Kazxu/Single-Pair-Ethernet-For-Industrial-Use/EVAL_ADIN1110/Core/Src/tcpecho_raw.c

/*
 * Copyright (c) 2001-2004 Swedish Institute of Computer Science.
 * All rights reserved. 
 * 
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
 * This file is part of and a contribution to the lwIP TCP/IP stack.
 *
 * Credits go to Adam Dunkels (and the current maintainers) of this software.
 *
 * Christiaan Simons rewrote this file to get a more stable echo example.
 */

/**
 * @file
 * TCP echo server example using raw API.
 *
 * Echos all bytes sent by connecting client,
 * and passively closes when client is done.
 *
 *
 *
 * EDITED FOR OUR BACHELOR USAGE, mixed code and etc - DAVY POON
 */

#include "lwip/opt.h"
#include "lwip/debug.h"
#include "lwip/stats.h"
#include "tcpecho_raw.h"
#include "lwip/opt.h"
#include "lwip/sys.h"
#include "main.h"

static u32_t last_send_time = 0;  // Timestamp of the last sent message

static char *EVAL_STRING_MSG = " \n YOUR MSG: TILKOBLET YAHOO \n" ;

struct tcp_pcb *global_tpcb = NULL;  // Definition of the global TCP control block
static char *shared_buffer = NULL; // Shared buffer between TCP Echo server and Main
#if LWIP_TCP && LWIP_CALLBACK_API




enum tcpecho_raw_states
{
  ES_NONE = 0,
  ES_ACCEPTED,
  ES_RECEIVED,
  ES_CLOSING
};

struct tcpecho_raw_state
{
  u8_t state;
  u8_t retries;
  struct tcp_pcb *pcb;
  /* pbuf (chain) to recycle */
  struct pbuf *p;
};

static void
tcpecho_raw_free(struct tcpecho_raw_state *es)
{
  if (es != NULL) {
    if (es->p) {
      /* free the buffer chain if present */
      pbuf_free(es->p);
    }

    mem_free(es);
  }  
}

static void
tcpecho_raw_close(struct tcp_pcb *tpcb, struct tcpecho_raw_state *es)
{
  tcp_arg(tpcb, NULL);
  tcp_sent(tpcb, NULL);
  tcp_recv(tpcb, NULL);
  tcp_err(tpcb, NULL);
  tcp_poll(tpcb, NULL, 0);

  tcpecho_raw_free(es);

  tcp_close(tpcb);
}

static void
tcpecho_raw_send(struct tcp_pcb *tpcb, struct tcpecho_raw_state *es)
{
  struct pbuf *ptr;
  err_t wr_err = ERR_OK;
 
  while ((wr_err == ERR_OK) &&
         (es->p != NULL) && 
         (es->p->len <= tcp_sndbuf(tpcb))) {
    ptr = es->p;

    /* enqueue data for transmission */
    wr_err = tcp_write(tpcb, ptr->payload, ptr->len, 1);
    if (wr_err == ERR_OK) {
      u16_t plen;

      plen = ptr->len;
      /* continue with next pbuf in chain (if any) */
      es->p = ptr->next;
      if(es->p != NULL) {
        /* new reference! */
        pbuf_ref(es->p);
      }
      /* chop first pbuf from chain */
      pbuf_free(ptr);
      /* we can read more data now */
      tcp_recved(tpcb, plen);
    } else if(wr_err == ERR_MEM) {
      /* we are low on memory, try later / harder, defer to poll */
      es->p = ptr;
    } else {
      /* other problem ?? */
    }
  }
}

static void
tcpecho_raw_error(void *arg, err_t err)
{
  struct tcpecho_raw_state *es;

  LWIP_UNUSED_ARG(err);

  es = (struct tcpecho_raw_state *)arg;

  tcpecho_raw_free(es);
}
// Define 'last_send_time'
// Function poll callback for the TCP echo server. Timer baserer seg til polling interval set i initialization.
static err_t tcpecho_raw_poll(void *arg, struct tcp_pcb *tpcb) {

	// Retrieve the state structure til current TCP connection, passed as 'arg' basert på default LWIP -raw API.
	struct tcpecho_raw_state *es = (struct tcpecho_raw_state *)arg;

	// Get the current system time in milliseconds from the lwIP system clock.
	u32_t current_time = sys_now();

    // Check if 500ms
    if (current_time - last_send_time >= 500) {


       // const char *msg = "Hello, this is a timed message! \n";
    	const char *msg = buffer;

        // Check if there is enough space in the TCP send buffer to send the message.
        if (tcp_sndbuf(tpcb) > strlen(msg)) {

        	 // Write the message to the TCP send buffer.
        	/* pcb: The TCP control block (PCB) -> Den init
			   data: Pointer to the data to be sent.
               len: Length of the data in bytes.
               flags: Control flag -> operation av tcp_write.*/
            tcp_write(tpcb, msg, strlen(msg), TCP_WRITE_FLAG_COPY);// Ensure that the message is actually sent out over the network.
            /*
             Efficient buffer management, including appropriate use of flags like TCP_WRITE_FLAG_COPY,
             is essential to ensure that your TCP/IP stack remains responsive and efficient,
             avoiding potential pitfalls like buffer overruns or unnecessary delays in data transmission.
             - https://lwip.fandom.com/wiki/Tuning_TCP
             */

            // Calls the internal lwIP function to process and send TCP packets.
            tcp_output(tpcb); //OUTPUT fra LWIP


            last_send_time = current_time;  // Update the last send time -> current time
        }
    }

    // Check if -> echo server state == not null, som betyr connection is still active
    if (es != NULL) {
    	 // Check if hvis pending data har ikke blitt sent.
        if (es->p != NULL) {
            // send remaining data
        	// Logic to send remaining data ikke blitt implementert enda
        	// "Typically, this would involve checking the TCP send buffer space and calling tcp_write as needed." - LWIP
        }
        // any additional handling --> HER KAN VI ADDE MER FUNKSJON
        // inkludert  connection maintenance, error checks, etc.

    } else { // If the state == null, problem med connection (e.g., it was unexpectedly closed).

    	// Abort the TCP connection to clean up the PCB and release resources.
        tcp_abort(tpcb);
        return ERR_ABRT;
    }
    // If everything processed correctly and the connection is still active, return ERR_OK.
    return ERR_OK;
}


static err_t
tcpecho_raw_sent(void *arg, struct tcp_pcb *tpcb, u16_t len)
{
  struct tcpecho_raw_state *es;

  LWIP_UNUSED_ARG(len);

  es = (struct tcpecho_raw_state *)arg;
  es->retries = 0;

  if(es->p != NULL) {
    /* still got pbufs to send */
    tcp_sent(tpcb, tcpecho_raw_sent);
    tcpecho_raw_send(tpcb, es);
  } else {
    /* no more pbufs to send */
    if(es->state == ES_CLOSING) {
      tcpecho_raw_close(tpcb, es);
    }
  }
  return ERR_OK;
}
static err_t
tcpecho_raw_recv(void *arg, struct tcp_pcb *tpcb, struct pbuf *p, err_t err) {
    struct tcpecho_raw_state *es;
    err_t ret_err;

    LWIP_ASSERT("arg != NULL", arg != NULL);
    es = (struct tcpecho_raw_state *)arg;

    if (p == NULL) {
        // Connection closed
        es->state = ES_CLOSING;
        if (es->p == NULL) {
            tcpecho_raw_close(tpcb, es);
        } else {
            tcpecho_raw_send(tpcb, es);
        }
        ret_err = ERR_OK;
    } else if (err != ERR_OK) {
        // Handle receive error
        if (p != NULL) {
            pbuf_free(p);
        }
        ret_err = err;
    } else {
        // Process received data
        if (es->state == ES_ACCEPTED) {
            es->state = ES_RECEIVED;
        }
        send_eval_string_msg(tpcb); // Send the EVAL_STRING_MSG

        // Echo logic as before
        if (es->p != NULL) {
            pbuf_cat(es->p, p);
        } else {
            es->p = p;
            pbuf_ref(p);
        }
        tcpecho_raw_send(tpcb, es);
        ret_err = ERR_OK;
    }
    return ret_err;
}


static err_t
tcpecho_raw_accept(void *arg, struct tcp_pcb *newpcb, err_t err)
{
  err_t ret_err;
  struct tcpecho_raw_state *es;

  LWIP_UNUSED_ARG(arg);
  if ((err != ERR_OK) || (newpcb == NULL)) {
    return ERR_VAL;
  }

  /* Unless this pcb should have NORMAL priority, set its priority now.
     When running out of pcbs, low priority pcbs can be aborted to create
     new pcbs of higher priority. */
  tcp_setprio(newpcb, TCP_PRIO_MIN);

  es = (struct tcpecho_raw_state *)mem_malloc(sizeof(struct tcpecho_raw_state));
  if (es != NULL) {
    es->state = ES_ACCEPTED;
    es->pcb = newpcb;
    es->retries = 0;
    es->p = NULL;
    /* pass newly allocated es to our callbacks */
    tcp_arg(newpcb, es);
    tcp_recv(newpcb, tcpecho_raw_recv);
    tcp_err(newpcb, tcpecho_raw_error);
    tcp_poll(newpcb, tcpecho_raw_poll, 0);
    tcp_sent(newpcb, tcpecho_raw_sent);
    ret_err = ERR_OK;
  } else {
    ret_err = ERR_MEM;
  }
  return ret_err;
}

// Initialization function to set up the PCB and polling
void tcpecho_raw_init(char *buffer) {
	//LAGER TCP  PCB -> TCP SOCKET
	shared_buffer = buffer;
    global_tpcb = tcp_new();
    if (global_tpcb != NULL) {  // Check if the PCB was successfully created.
        err_t err = tcp_bind(global_tpcb, IP_ADDR_ANY, 66);
        // Bind the newly created PCB object to any IP address on port 66.

        if (err == ERR_OK) {// Check if the binding was successful.

        	// Putter PCB == LISTEN state, convert til listen PCB -> accept incoming connections.
        	global_tpcb = tcp_listen(global_tpcb);

        	 // Set up a callback function som event handler -> incoming connections.
        	 // `tcp_accept` assigns a function to be called when a new connection is established.
            tcp_accept(global_tpcb, tcpecho_raw_accept);

            // Set up a callback function to be called periodically
            // polling callback brukt som regularly check/event handle tasks som å  sende periodic/timed messages
            // The `1` = polling frequency; in the lwIP stack ->> multiplied av TCP timer interval
            // (typically 500 ms), so a value of `1`  = 500 ms.
            tcp_poll(global_tpcb, tcpecho_raw_poll, 1);  // Set the poll interval
        }
    }
}



void send_eval_string_msg(struct tcp_pcb *tpcb) {
    if (tpcb != NULL && tcp_sndbuf(tpcb) > strlen(EVAL_STRING_MSG)) {
        tcp_write(tpcb, EVAL_STRING_MSG, strlen(EVAL_STRING_MSG), TCP_WRITE_FLAG_COPY);
        tcp_output(tpcb);  // Data sendt Instant, brukes kanskje senere, vet ikke, har bare med tilfelle
    }
}



#endif /* LWIP_TCP && LWIP_CALLBACK_API */
