Kazxu/Single-Pair-Ethernet-For-Industrial-Use/EVAL_ADIN1110/Core/Src/usart.c

/**
  ******************************************************************************
  * File Name          : USART.c
  * Description        : This file provides code for the configuration
  *                      of the USART instances.
  ******************************************************************************
  * @attention
  *
  * <h2><center>&copy; Copyright (c) 2020 STMicroelectronics.
  * All rights reserved.</center></h2>
  *
  * This software component is licensed by ST under BSD 3-Clause license,
  * the "License"; You may not use this file except in compliance with the
  * License. You may obtain a copy of the License at:
  *                        opensource.org/licenses/BSD-3-Clause
  *
  ******************************************************************************
  */

/**
  *  Portions Copyright (c) 2020, 2021 Analog Devices, Inc.
  */

/* Includes ------------------------------------------------------------------*/
#include "usart.h"

UART_HandleTypeDef huart1;
DMA_HandleTypeDef hdma_usart1_tx;
DMA_HandleTypeDef hdma_usart1_rx;
/* USART1 init function */

HAL_StatusTypeDef MX_USART1_UART_Init(void)
{

  huart1.Instance = USART1;
  huart1.Init.BaudRate = 115200;
  huart1.Init.WordLength = UART_WORDLENGTH_8B;
  huart1.Init.StopBits = UART_STOPBITS_1;
  huart1.Init.Parity = UART_PARITY_NONE;
  huart1.Init.Mode = UART_MODE_TX_RX;
  huart1.Init.HwFlowCtl = UART_HWCONTROL_NONE;
  huart1.Init.OverSampling = UART_OVERSAMPLING_16;
  huart1.Init.OneBitSampling = UART_ONE_BIT_SAMPLE_DISABLE;
  huart1.Init.ClockPrescaler = UART_PRESCALER_DIV1;
  huart1.AdvancedInit.AdvFeatureInit = UART_ADVFEATURE_NO_INIT;

  return HAL_UART_Init(&huart1);
}

void HAL_UART_MspInit(UART_HandleTypeDef* uartHandle)
{

  GPIO_InitTypeDef GPIO_InitStruct = {0};
  if(uartHandle->Instance==USART1)
  {
    /* USART1 clock enable */
    __HAL_RCC_USART1_CLK_ENABLE();

    /**USART1 GPIO Configuration
    PA10     ------> USART1_RX
    PA9     ------> USART1_TX
    */
    GPIO_InitStruct.Pin = GPIO_PIN_10|GPIO_PIN_9;
    GPIO_InitStruct.Mode = GPIO_MODE_AF_PP;
    GPIO_InitStruct.Pull = GPIO_NOPULL;
    GPIO_InitStruct.Speed = GPIO_SPEED_FREQ_VERY_HIGH;
    GPIO_InitStruct.Alternate = GPIO_AF7_USART1;
    HAL_GPIO_Init(GPIOA, &GPIO_InitStruct);

  /* USER CODE BEGIN USART1_MspInit 1 */
 /* NVIC for USART, to catch the TX complete */
  HAL_NVIC_SetPriority(USART1_IRQn, 1, 1);
  HAL_NVIC_EnableIRQ(USART1_IRQn);
  /* USER CODE END USART1_MspInit 1 */

  }
}

void HAL_UART_MspDeInit(UART_HandleTypeDef* uartHandle)
{

  if(uartHandle->Instance==USART1)
  {
    /* Peripheral clock disable */
    __HAL_RCC_USART1_CLK_DISABLE();

    /**USART1 GPIO Configuration
    PA10     ------> USART1_RX
    PA9     ------> USART1_TX
    */
    HAL_GPIO_DeInit(GPIOA, GPIO_PIN_10|GPIO_PIN_9);

    /* USART1 DMA DeInit */
    HAL_DMA_DeInit(uartHandle->hdmatx);
    HAL_DMA_DeInit(uartHandle->hdmarx);
  }
}
/* USER CODE BEGIN 1 */

HAL_StatusTypeDef submitRxBuffer (uint8_t * buffer, int nbBytes)
{

  return HAL_UART_Receive_IT(&huart1, (uint8_t *)buffer, nbBytes);
}

HAL_StatusTypeDef submitTxBuffer (uint8_t * buffer, int nbBytes)
{

  return HAL_UART_Transmit(&huart1, (uint8_t*)buffer, nbBytes,5);
}

/**
  * @brief  Rx Transfer completed callback
  * @param  UartHandle: UART handle
  * @note   This example shows a simple way to report end of DMA Rx transfer, and
  *         you can add your own implementation.
  * @retval None
  */
void HAL_UART_RxCpltCallback(UART_HandleTypeDef *UartHandle)
{
}

void HAL_UART_ErrorCallback(UART_HandleTypeDef *UartHandle)
{
}
/* USER CODE END 1 */

/************************ (C) COPYRIGHT STMicroelectronics *****END OF FILE****/
